exyn/FS-MFD/Misc/enclosure2.jpg

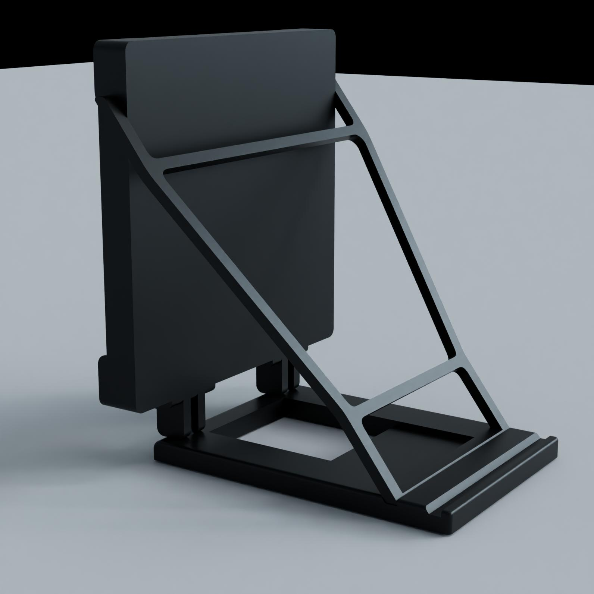
Misc/enclosure2.jpg
