exyn/FS-MFD/Misc/enclosure.jpg

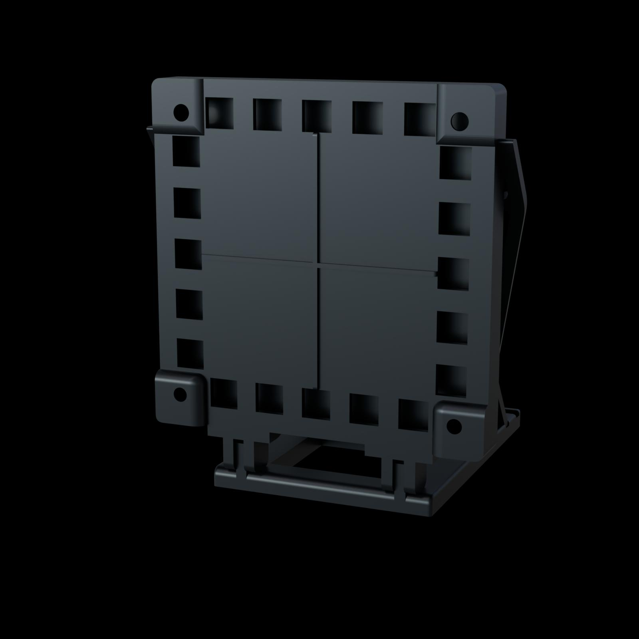
Misc/enclosure.jpg
