exyn/FS-MFD/Misc/FS-MFD Mechanics Part.png

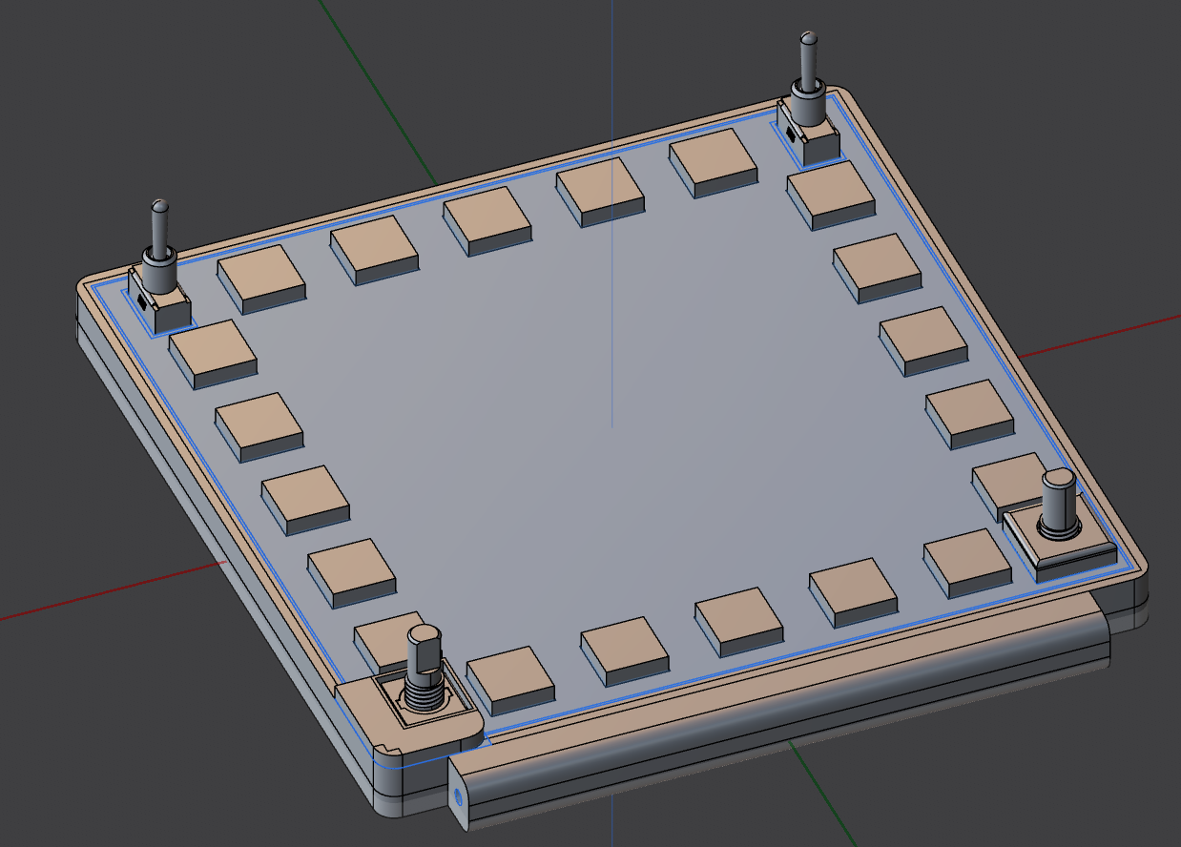
Misc/FS-MFD Mechanics Part.png
